vector76/gridfinity_openscad/Renders/divided_cup_2x1x2x5.stl

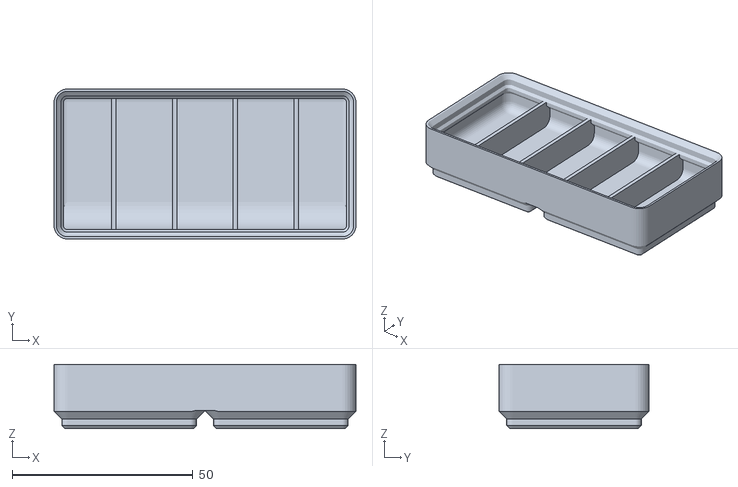
[picture p26: CAD file, 2022-11-13]
Renders/divided_cup_2x1x2x5.stl
83.5 x 41.5 x 17.8
