vector76/gridfinity_openscad/Renders/socket_holder_metric_stacking.stl

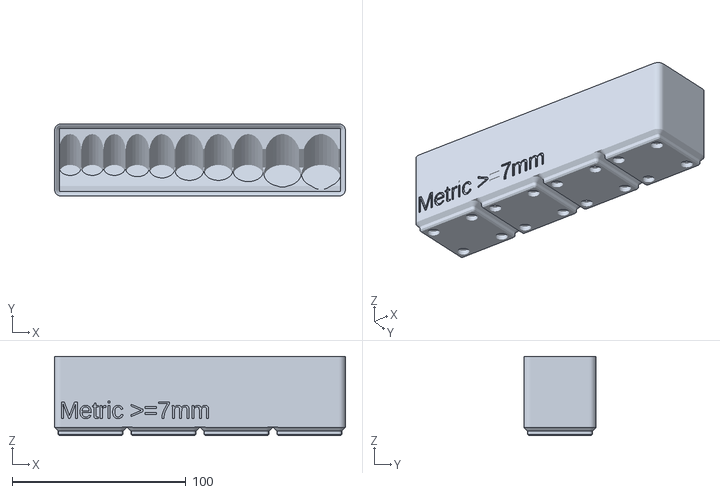
[picture p27: CAD file, 2022-11-13]
Renders/socket_holder_metric_stacking.stl
167.5 x 41.5 x 45.8
