vector76/gridfinity_openscad/Renders/filled_block_2x1x3x5.stl

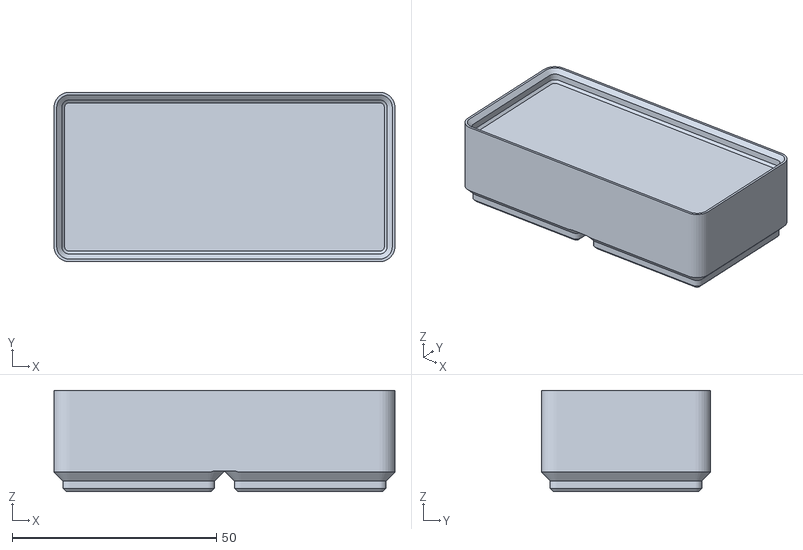
[picture p28: CAD file, 2022-11-13]
Renders/filled_block_2x1x3x5.stl
83.5 x 41.5 x 24.8
