vector76/gridfinity_openscad/Renders/base_lid.stl

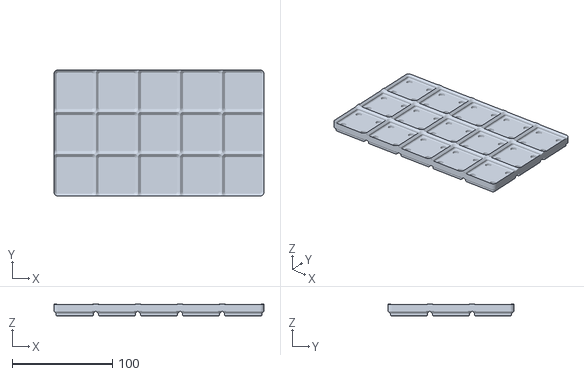
[picture p29: CAD file, 2022-11-13]
Renders/base_lid.stl
209.5 x 125.5 x 12.0
