vector76/gridfinity_openscad/Renders/socket_holder_imperial_small.stl

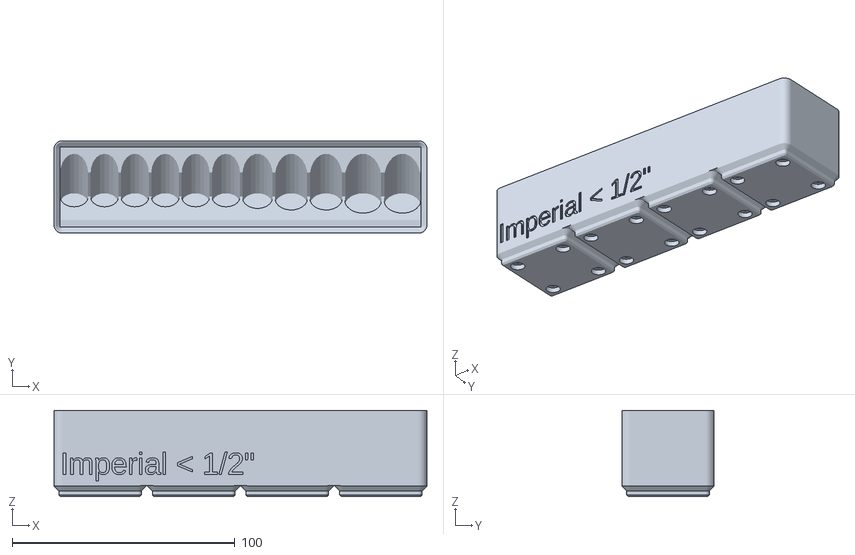
[picture p30: CAD file, 2022-11-13]
Renders/socket_holder_imperial_small.stl
167.5 x 41.5 x 38.8
