vector76/gridfinity_openscad/Renders/socket_holder_imperial_big.stl

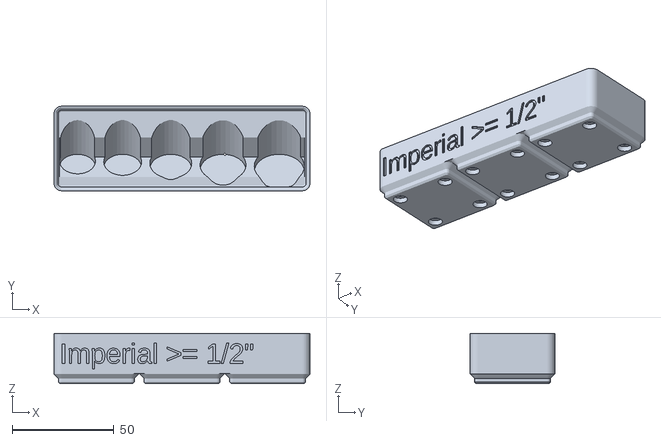
[picture p31: CAD file, 2022-11-13]
Renders/socket_holder_imperial_big.stl
125.5 x 41.5 x 24.8
