vector76/gridfinity_openscad/Renders/weighted_baseplate.stl

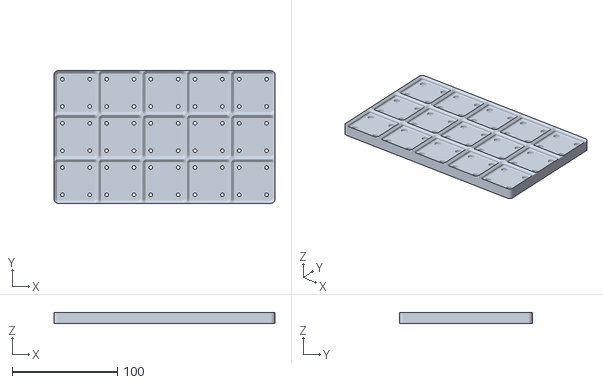
[picture p32: CAD file, 2022-09-25]
Renders/weighted_baseplate.stl
210.0 x 126.0 x 10.8
