vector76/gridfinity_openscad/Renders/baseplate.stl

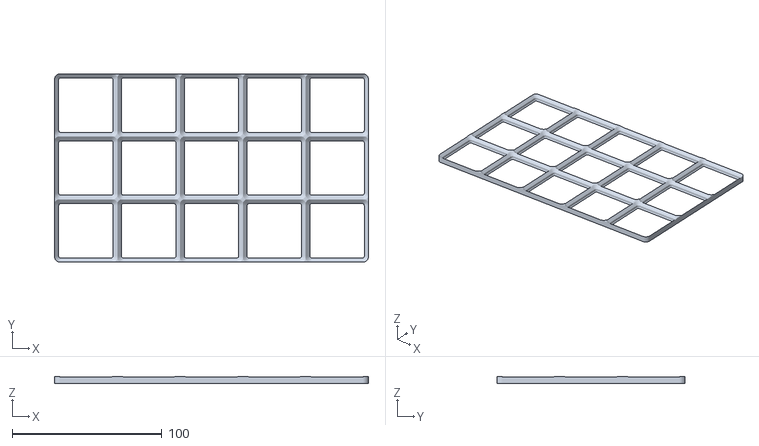
[picture p33: CAD file, 2022-09-25]
Renders/baseplate.stl
210.0 x 126.0 x 5.00
