vector76/gridfinity_openscad/Renders/flsun_q5.stl

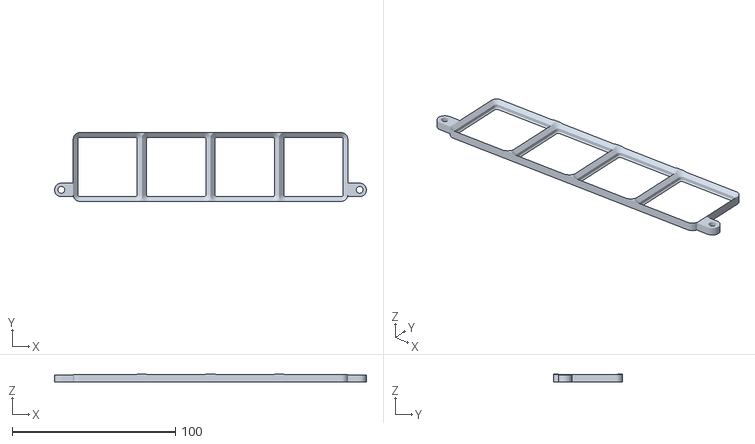
[picture p34: CAD file, 2022-09-25]
Renders/flsun_q5.stl
190.9 x 42.0 x 5.00
