vector76/gridfinity_openscad/gridfinity_cup_modules.scad

include <gridfinity_modules.scad>

// X dimension subdivisions
default_chambers = 1;

// Include overhang for labeling
default_withLabel = "disabled"; //[disabled: no label, left: left aligned label, right: right aligned label, center: center aligned label, leftchamber: left aligned chamber label, rightchamber: right aligned chamber label, centerchamber: center aligned chamber label]
// Width of the label in number of units, or zero for full width
default_labelWidth = 0; // 0.01
// Include larger corner fillet
default_fingerslide = true;
// Set magnet diameter and depth to 0 to print without magnet holes
// (Zack's design uses magnet diameter of 6.5)
default_magnet_diameter = 6.5;  // .1
// (Zack's design uses depth of 6)
default_screw_depth = 6;
// Minimum thickness above cutouts in base (Zack's design is effectively 1.2)
default_floor_thickness = 1.2;
// Thickness of outer walls (Zack's design is 0.95 mm)
default_wall_thickness = 0.95;
// Use rectangular inset for better bridging/printability
default_hole_overhang_remedy = false;
// Save material with thinner floor (only if no magnets, screws, or finger-slide used)
default_efficient_floor = false;
// Half-pitch base pads for offset stacking
default_half_pitch = false;
// Might want to remove inner lip of cup
default_lip_style = "normal";
// Limit attachments (magnets and scres) to box corners for faster printing.
box_corner_attachments_only = false;
basic_cup(
  num_x=2,
  num_y=1,
  num_z=3,
  chambers=default_chambers,
  withLabel=default_withLabel,
  labelWidth=default_labelWidth,
  magnet_diameter=default_magnet_diameter,
  screw_depth=default_screw_depth,
  floor_thickness=default_floor_thickness,
  wall_thickness=default_wall_thickness,
  hole_overhang_remedy=default_hole_overhang_remedy,
  efficient_floor=default_efficient_floor,
  half_pitch=default_half_pitch,
  lip_style=default_lip_style,
  box_corner_attachments_only=box_corner_attachments_only
);


// It's recommended that all parameters other than x, y, z size should be specified by keyword 
// and not by position.  The number of parameters makes positional parameters error prone, and
// additional parameters may be added over time and break things.
module basic_cup(
  num_x,
  num_y,
  num_z,
  chambers=default_chambers,
  withLabel=default_withLabel,
  labelWidth=default_labelWidth,
  fingerslide=default_fingerslide,
  magnet_diameter=default_magnet_diameter,
  screw_depth=default_screw_depth,
  floor_thickness=default_floor_thickness,
  wall_thickness=default_wall_thickness,
  hole_overhang_remedy=default_hole_overhang_remedy,
  efficient_floor=default_efficient_floor,
  half_pitch=default_half_pitch,
  lip_style=default_lip_style,
  box_corner_attachments_only=box_corner_attachments_only
  ) {
  num_separators = chambers-1;
  sep_pitch = num_x/(num_separators+1);
  separator_positions = num_separators < 1 ? [] : [ for (i=[1:num_separators]) i*sep_pitch ];
  
  difference() {
    grid_block(num_x, num_y, num_z, magnet_diameter, screw_depth, hole_overhang_remedy=hole_overhang_remedy, half_pitch=half_pitch, box_corner_attachments_only=box_corner_attachments_only);
    color("red") partitioned_cavity(num_x, num_y, num_z, withLabel=withLabel,
    labelWidth=labelWidth, fingerslide=fingerslide, magnet_diameter=magnet_diameter, 
    screw_depth=screw_depth, floor_thickness=floor_thickness, wall_thickness=wall_thickness,
    efficient_floor=efficient_floor, separator_positions=separator_positions, lip_style=lip_style);
  }
}


// separator positions are defined in units from the left side
module irregular_cup(
  num_x,
  num_y,
  num_z,
  withLabel=default_withLabel,
  labelWidth=default_labelWidth,
  fingerslide=default_fingerslide,
  magnet_diameter=default_magnet_diameter,
  screw_depth=default_screw_depth,
  floor_thickness=default_floor_thickness,
  wall_thickness=default_wall_thickness,
  hole_overhang_remedy=default_hole_overhang_remedy,
  efficient_floor=default_efficient_floor,
  half_pitch=default_half_pitch,
  separator_positions=[],
  lip_style=default_lip_style
  ) {
  difference() {
    grid_block(num_x, num_y, num_z, magnet_diameter, screw_depth, hole_overhang_remedy=hole_overhang_remedy, half_pitch=half_pitch, box_corner_attachments_only=box_corner_attachments_only);
    color("red") partitioned_cavity(num_x, num_y, num_z, withLabel=withLabel,
    labelWidth=labelWidth, fingerslide=fingerslide, magnet_diameter=magnet_diameter, 
    screw_depth=screw_depth, floor_thickness=floor_thickness, wall_thickness=wall_thickness,
    efficient_floor=efficient_floor, separator_positions=separator_positions, lip_style=lip_style);
  }
}


module partitioned_cavity(num_x, num_y, num_z, withLabel=default_withLabel, 
    labelWidth=default_labelWidth, fingerslide=default_fingerslide, 
    magnet_diameter=default_magnet_diameter, screw_depth=default_screw_depth, 
    floor_thickness=default_floor_thickness, wall_thickness=default_wall_thickness,
    efficient_floor=default_efficient_floor, separator_positions=[], lip_style=default_lip_style) {
  // cavity with removed segments so that we leave dividing walls behind
  gp = gridfinity_pitch;
  outer_wall_th = 1.8;  // cavity is this far away from the 42mm 'ideal' block
  inner_wall_th =1.2;
    
  bar_d = 1.2;
  zpoint = gridfinity_zpitch*num_z;
  
  yz = [[ (num_y-0.5)*gridfinity_pitch-14, zpoint-bar_d/2 ],
    [ (num_y-0.5)*gridfinity_pitch, zpoint-bar_d/2 ],
    [ (num_y-0.5)*gridfinity_pitch, zpoint-bar_d/2-10.18 ]
  ];
  
  cavity_xsize = gp*num_x-2*outer_wall_th;

  difference() {
    basic_cavity(num_x, num_y, num_z, fingerslide=fingerslide, magnet_diameter=magnet_diameter,
    screw_depth=screw_depth, floor_thickness=floor_thickness, wall_thickness=wall_thickness,
    efficient_floor=efficient_floor, lip_style=lip_style);
    
    if (len(separator_positions) > 0) {
      for (i=[0:len(separator_positions)-1]) {
        translate([gp*(-0.5+separator_positions[i])-inner_wall_th/2, -gp/2, 0]) cube([inner_wall_th, gp*num_y, gridfinity_zpitch*(num_z+1)]);
      }
    }
    
    // this is the label
    if (withLabel != "disabled") {
      // calcualte list of chambers. 
      chamberWidths = len(separator_positions) < 1 || 
        labelWidth == 0 ||
        withLabel == "left" ||
        withLabel == "center" ||
        withLabel == "right" ?
        [ num_x ] // single chamber equal to the bin length
        : [ for (i=[0:len(separator_positions)]) (i==len(separator_positions) ? num_x : separator_positions[i]) - (i==0 ? 0 : separator_positions[i-1]) ];
        
      for (i=[0:len(chamberWidths)-1]) {
        chamberStart = i == 0 ? 0 : separator_positions[i-1];
        chamberWidth = chamberWidths[i];
        label_num_x = (labelWidth == 0 || labelWidth > chamberWidth) ? chamberWidth : labelWidth;
        label_pos_x = (withLabel == "center" || withLabel == "centerchamber" )? (chamberWidth - label_num_x) / 2 
                        : (withLabel == "right" || withLabel == "rightchamber" )? chamberWidth - label_num_x 
                        : 0 ;

        hull() for (i=[0,1, 2])
        translate([(-gridfinity_pitch/2) + ((chamberStart + label_pos_x) * gridfinity_pitch), yz[i][0], yz[i][1]])
        rotate([0, 90, 0])
        union(){
            tz(abs(label_num_x)*gridfinity_pitch)
            sphere(d=bar_d, $fn=24);
            sphere(d=bar_d, $fn=24);
        }
      }
    }
  }
}


module basic_cavity(num_x, num_y, num_z, fingerslide=default_fingerslide, 
    magnet_diameter=default_magnet_diameter, screw_depth=default_screw_depth, 
    floor_thickness=default_floor_thickness, wall_thickness=default_wall_thickness,
    efficient_floor=default_efficient_floor, lip_style=default_lip_style) {
  eps = 0.1;
  // I couldn't think of a good name for this ('q') but effectively it's the
  // size of the overhang that produces a wall thickness that's less than the lip
  // arount the top inside edge.
  q = 1.65-wall_thickness+0.95;  // default 1.65 corresponds to wall thickness of 0.95
  q2 = 0.1;
  inner_lip_ht = 1.2;
  part_ht = 5;  // height of partition between cells
  // the Z height of the bottom of the inside edge of the standard lip
  zpoint = max(part_ht+floor_thickness, gridfinity_zpitch*num_z-inner_lip_ht);
  facets = 13;
  mag_ht = magnet_diameter > 0 ? 2.4: 0;
  m3_ht = screw_depth;
  efloor = efficient_floor && magnet_diameter == 0 && screw_depth == 0 && !fingerslide;
  seventeen = gridfinity_pitch/2-4;
  
  floorht = max(mag_ht, m3_ht, part_ht) + floor_thickness;
  
  // replace "normal" with "reduced" if z-height is less than 1.8
  lip_style2 = (num_z < 1.8 && lip_style == "normal") ? "reduced" : lip_style;
  // replace "reduced" with "none" if z-height is less than 1.1
  lip_style3 = (num_z < 1.2 && lip_style2 == "reduced") ? "none" : lip_style2;
  
  difference() {
    union() {
      // cut out inside edge of standard lip
      hull() cornercopy(seventeen, num_x, num_y) {
        tz(zpoint-eps) cylinder(d=2.3, h=inner_lip_ht+2*eps, $fn=24); // lip
      }
      
      hull() cornercopy(seventeen, num_x, num_y) {
        // create bevels below the lip
        if (lip_style3 == "reduced") {
          tz(zpoint+1.8) cylinder(d=3.7, h=0.1, $fn=32); // transition from lip (where top of lip would be) ...
          // radius increases by (2.3+2*q-3.7)/2 = q-1.4/2 = q-0.7
          tz(zpoint-(q-0.7)+1.9-q2) cylinder(d=2.3+2*q, h=q2, $fn=32);   // ... to top of thin wall ...
        }
        else if (lip_style3 == "none") {
          tz(zpoint) cylinder(d=2.3+2*q, h=6, $fn=32);   // remove entire lip
        }
        else {  // normal
          tz(zpoint-0.1) cylinder(d=2.3, h=0.1, $fn=24);       // transition from lip ...
          tz(zpoint-q-q2) cylinder(d=2.3+2*q, h=q2, $fn=32);   // ... to top of thin wall ...
        }
        // create rounded bottom of bowl (8.5 is high enough to not expose gaps)
        tz(2.3/2+q+floorht) sphere(d=2.3+2*q, $fn=32);       // .. to bottom of thin wall and floor
        tz(2.3/2+q+floorht) mirror([0, 0, 1]) cylinder(d1=2.3+2*q, d2=0, h=1.15+q, $fn=32);
      }
    }
    
    // cut away from the negative to leave behind wall to make it easier to remove piece
    pivot_z = 13.6-0.45+floorht-5+seventeen-17;
    pivot_y = -10;
    
    // rounded inside bottom
    if(fingerslide){
      for (ai=[0:facets-1])
        // normal slide position is -seventeen-1.15 which is the edge of the inner lip
        // reduced slide position is -seventeen-1.85 which is the edge of the upper lip
        // no lip means we need -gridfinity_pitch/2+1.5+0.25+wall_thickness ?
        translate([0, (
          lip_style3 == "reduced" ? -0.7 
          : (lip_style3=="none" ? seventeen+1.15-gridfinity_pitch/2+0.25+wall_thickness
          : 0
          ) ), 0])
        translate([0, pivot_y, pivot_z])
        rotate([90*ai/(facets-1), 0, 0])
        translate([0, -pivot_y, -pivot_z])
        translate([-gridfinity_pitch/2, -10-seventeen-1.15, 0]) 
        cube([gridfinity_pitch*num_x, 10, gridfinity_zpitch*num_z+5]);
    }
  }
  
  // cut away side lips if num_x is less than 1
  if (num_x < 1) {
    hull() for (x=[-gridfinity_pitch/2+1.5+0.25+wall_thickness, -gridfinity_pitch/2+num_x*gridfinity_pitch-1.5-0.25-wall_thickness])
    for (y=[-10, (num_y-0.5)*gridfinity_pitch-seventeen])
    translate([x, y, (floorht+7*num_z)/2])
    cylinder(d=3, h=7*num_z, $fn=24);
  }
  
  if (efloor) {
    if (num_x < 1) {
      gridcopy(1, num_y) {
        tz(floor_thickness) intersection() {
          hull() cornercopy(seventeen-0.5) cylinder(r=1, h=5, $fn=32);
          translate([gridfinity_pitch*(-1+num_x), 0, 0]) hull() cornercopy(seventeen-0.5) cylinder(r=1, h=5, $fn=32);
        }
      
        // tapered top portion
        intersection() {
          hull() {
            tz(3) cornercopy(seventeen-0.5) cylinder(r=1, h=1, $fn=32);
            tz(5) cornercopy(seventeen+2.5-1.15-q) cylinder(r=1.15+q, h=4, $fn=32);
          }
          translate([gridfinity_pitch*(-1+num_x), 0, 0]) hull() {
            tz(3) cornercopy(seventeen-0.5) cylinder(r=1, h=1, $fn=32);
            tz(5) cornercopy(seventeen+2.5-1.15-q) cylinder(r=1.15+q, h=4, $fn=32);
          }
        }
      }
    }
    else {
      // establishes floor
      gridcopy(num_x, num_y) hull() tz(floor_thickness) cornercopy(seventeen-0.5) cylinder(r=1, h=5, $fn=32);
      
      // tapered top portion
      gridcopy(num_x, num_y) hull() {
        tz(3) cornercopy(seventeen-0.5) cylinder(r=1, h=1, $fn=32);
        tz(5-(+2.5-1.15-q)) cornercopy(seventeen) cylinder(r=1.15+q, h=4, $fn=32);
      }
    }
  }
}


module tz(z) {
  translate([0, 0, z]) children();
}
